JimothyJohn/wafer-flower/stl/dxf/02b_tail.dxf

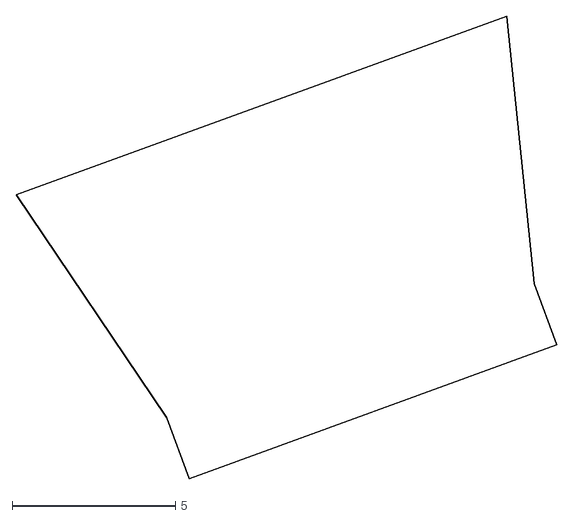
[picture p17: CAD file, 2026-07-26]
stl/dxf/02b_tail.dxf
16.6 x 14.2
