JimothyJohn/wafer-flower/stl/step/pinion.stp

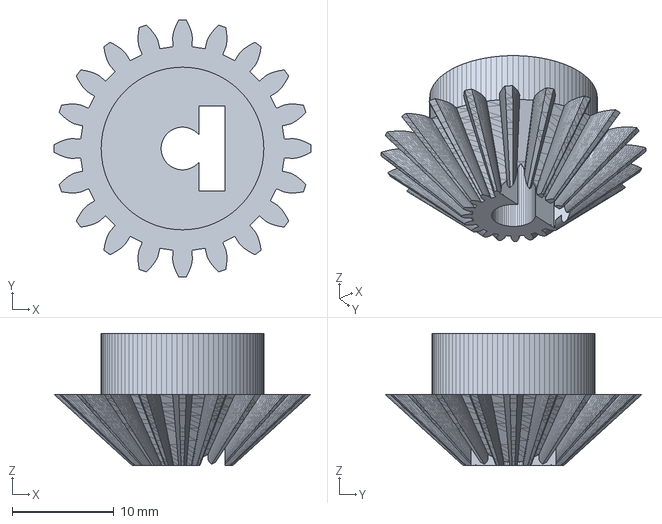
[picture p18: CAD file, 2026-07-28]
stl/step/pinion.stp
25.3 x 25.3 x 13.0 mm
