JimothyJohn/wafer-flower/stl/dxf/03_socket.dxf

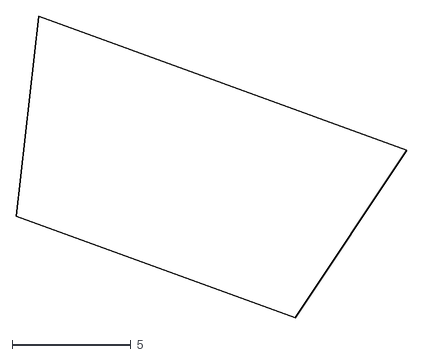
[picture p19: CAD file, 2026-07-20]
stl/dxf/03_socket.dxf
16.4 x 12.7
