JimothyJohn/wafer-flower/stl/segment_pair.stl

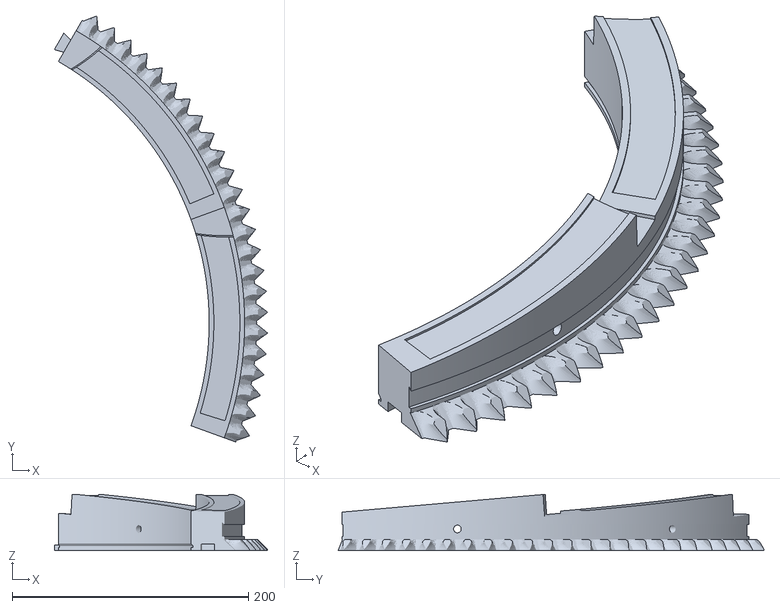
[picture p20: CAD file, 2026-07-28]
stl/segment_pair.stl
180.5 x 360.3 x 47.7
