JimothyJohn/wafer-flower/stl/step/bracket_bottom.stp

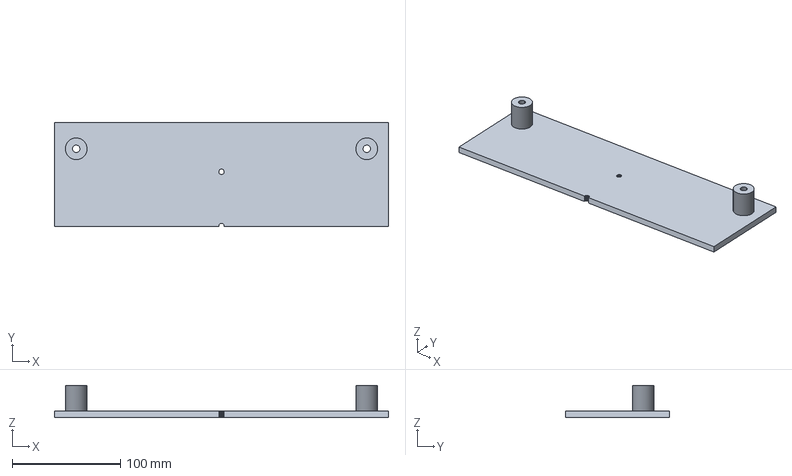
[picture p21: CAD file, 2026-07-27]
stl/step/bracket_bottom.stp
307.9 x 96.0 x 29.8 mm
