JimothyJohn/wafer-flower/stl/dxf/04_pocket.dxf

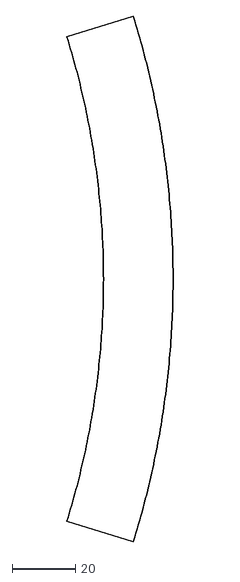
[picture p22: CAD file, 2026-07-20]
stl/dxf/04_pocket.dxf
33.6 x 166.1
