JimothyJohn/wafer-flower/stl/step/bracket_plate.stp

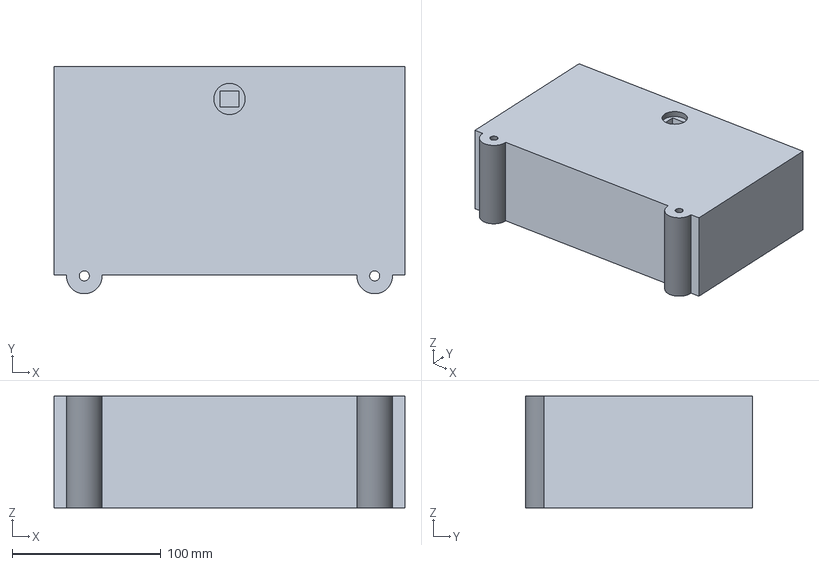
[picture p23: CAD file, 2026-07-26]
stl/step/bracket_plate.stp
236.0 x 153.0 x 75.2 mm
