JimothyJohn/wafer-flower/stl/halo_frame.stl

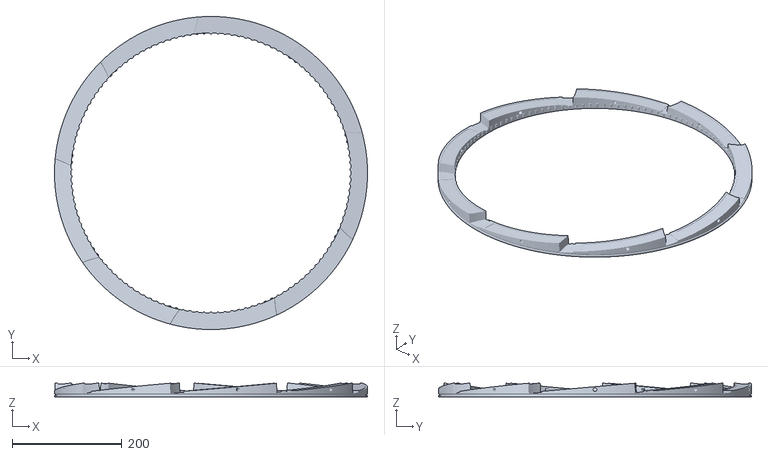
[picture p24: CAD file, 2026-07-25]
stl/halo_frame.stl
570.0 x 570.0 x 25.0
