JimothyJohn/wafer-flower/stl/step/segment.stp

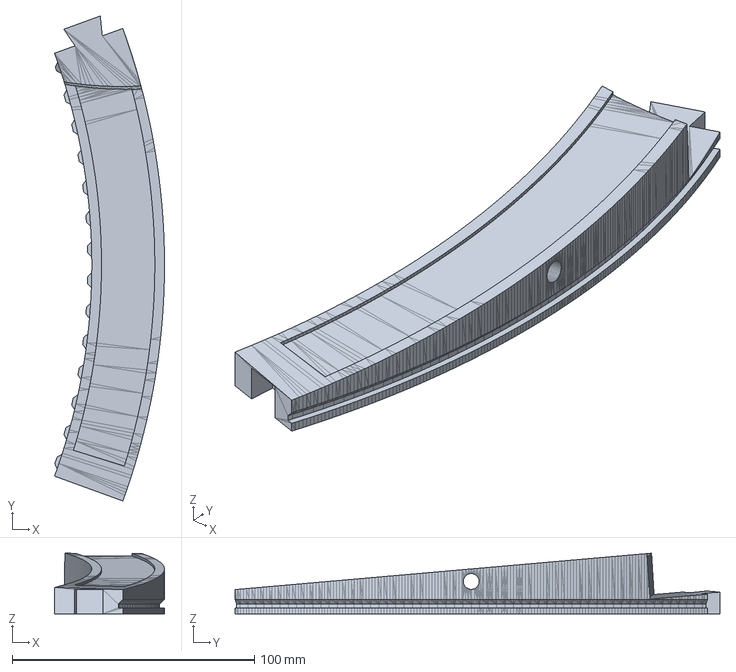
[picture p25: CAD file, 2026-07-25]
stl/step/segment.stp
45.4 x 200.1 x 25.0 mm
