JimothyJohn/wafer-flower/stl/bracket_fitcheck.stl

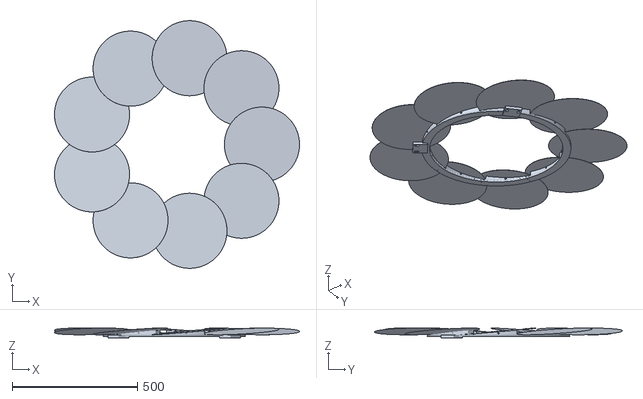
[picture p26: CAD file, 2026-07-25]
stl/bracket_fitcheck.stl
978.8 x 989.3 x 39.5
