JimothyJohn/wafer-flower/stl/step/wafer.stp

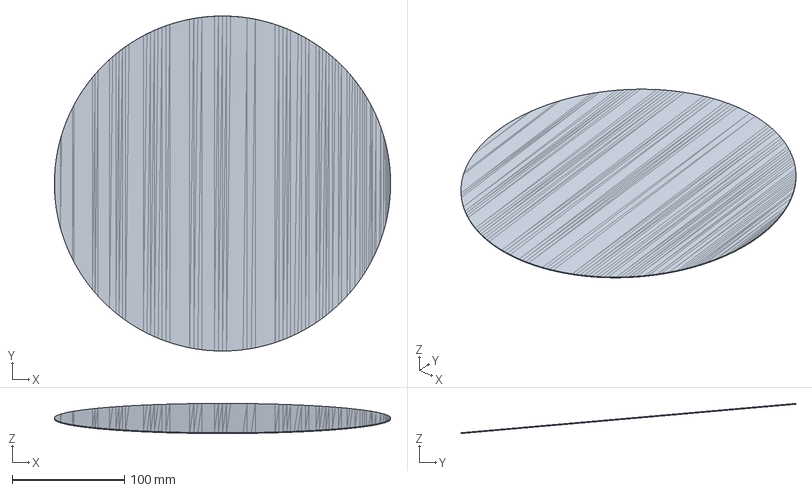
[picture p27: CAD file, 2026-07-23]
stl/step/wafer.stp
300.0 x 298.9 x 26.9 mm
