JimothyJohn/wafer-flower/docs/models/segment.stl

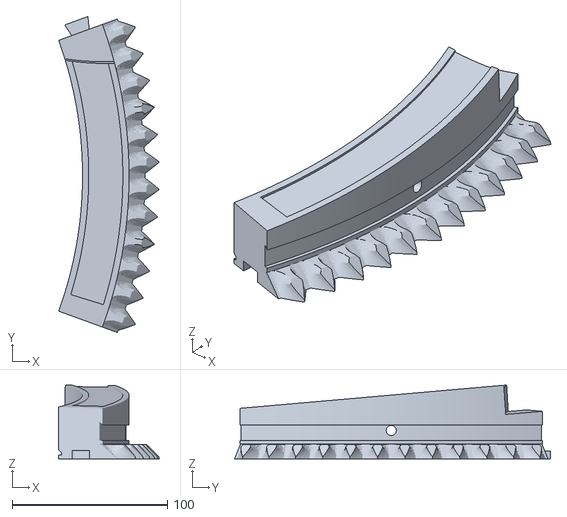
[picture p28: CAD file, 2026-07-28]
docs/models/segment.stl
64.9 x 203.6 x 47.7
