JimothyJohn/wafer-flower/docs/models/my_frame_segment.stl

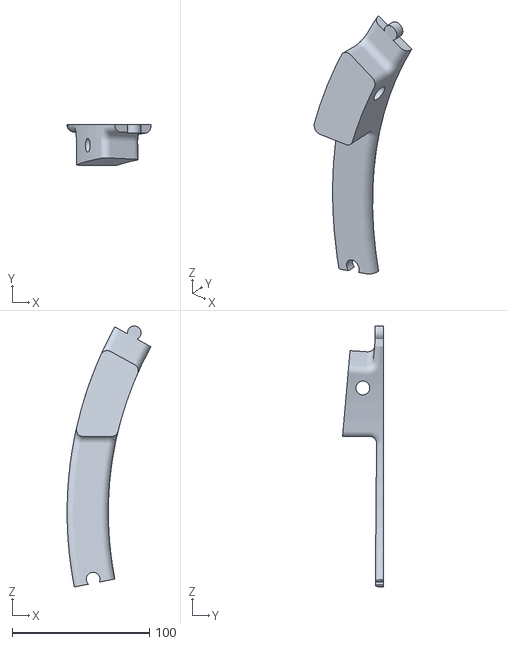
[picture p29: CAD file, 2026-07-22]
docs/models/my_frame_segment.stl
61.0 x 29.8 x 189.9
