JimothyJohn/wafer-flower/stl/drive_clamp.stl

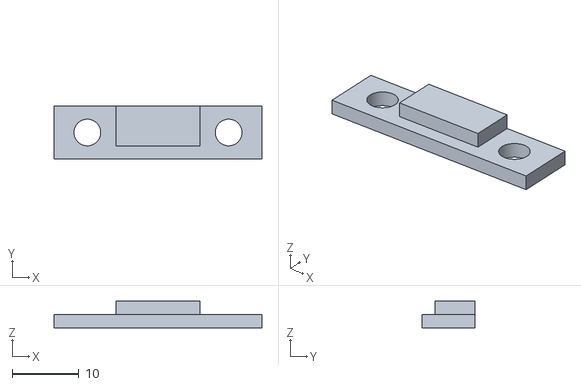
[picture p30: CAD file, 2026-07-23]
stl/drive_clamp.stl
31.2 x 8.00 x 4.00
