JimothyJohn/wafer-flower/stl/drive_plate.stl

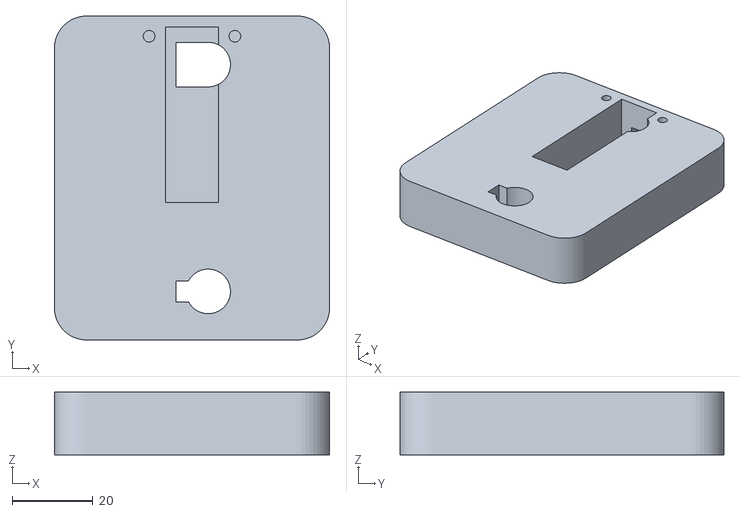
[picture p31: CAD file, 2026-07-23]
stl/drive_plate.stl
68.0 x 80.0 x 15.5
