JimothyJohn/wafer-flower/stl/drive_pinion.stl

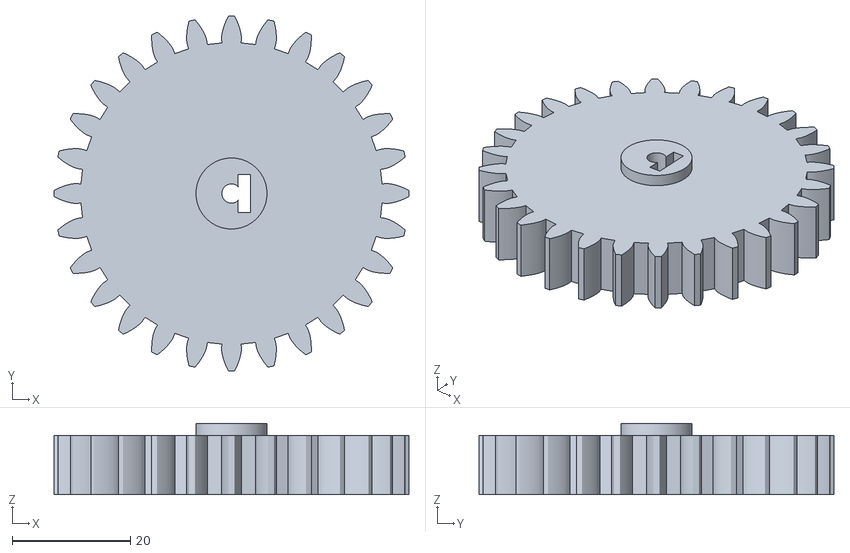
[picture p32: CAD file, 2026-07-23]
stl/drive_pinion.stl
60.0 x 60.0 x 12.0
