JimothyJohn/wafer-flower/stl/drive_fitcheck.stl

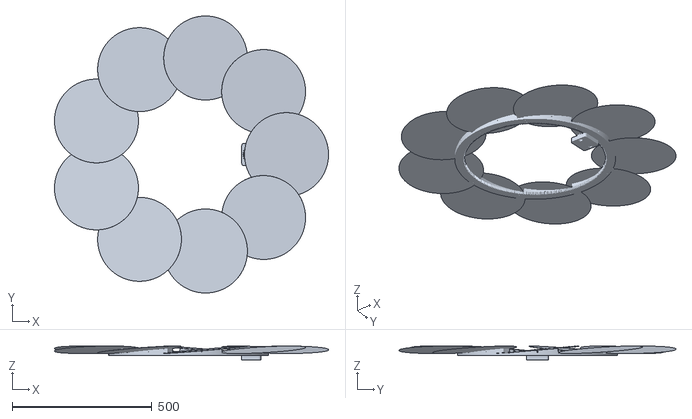
[picture p33: CAD file, 2026-07-23]
stl/drive_fitcheck.stl
978.8 x 989.3 x 50.0
