JimothyJohn/wafer-flower/docs/media/step1_segment.png

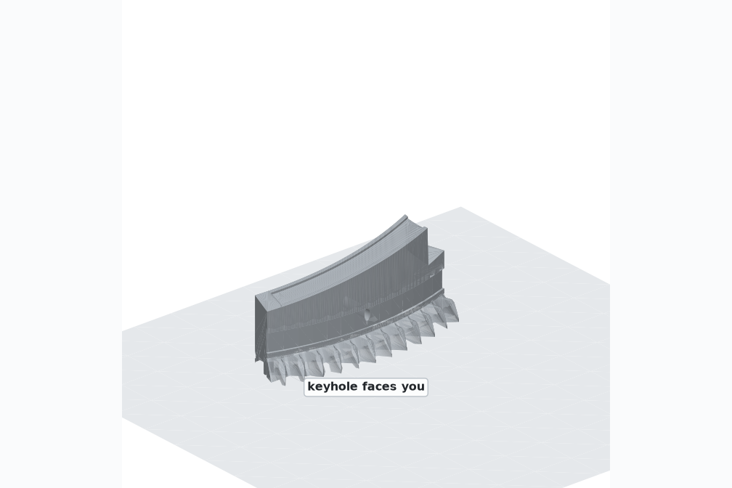
docs/media/step1_segment.png
