JimothyJohn/wafer-flower/docs/media/step3_outboard.png

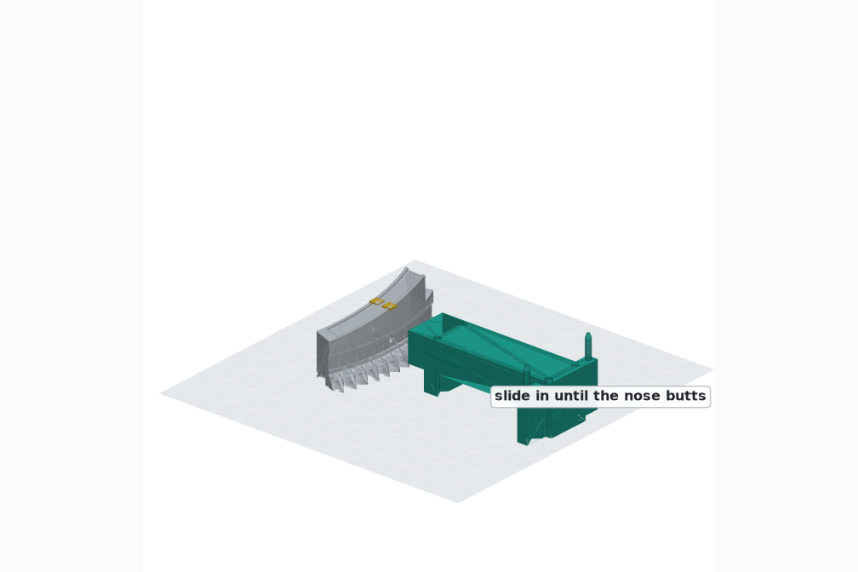
docs/media/step3_outboard.png
