JimothyJohn/wafer-flower/docs/media/step4_inboard.png

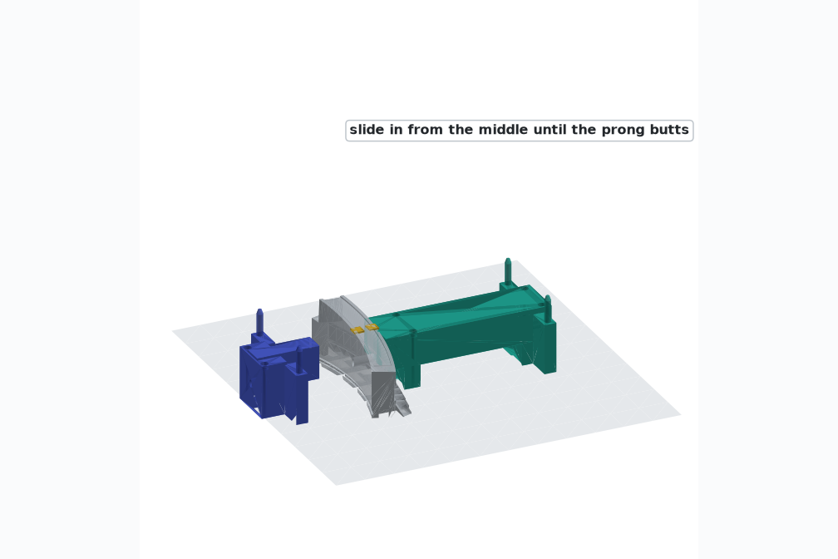
docs/media/step4_inboard.png
