JimothyJohn/wafer-flower/docs/media/step6_wafer.png

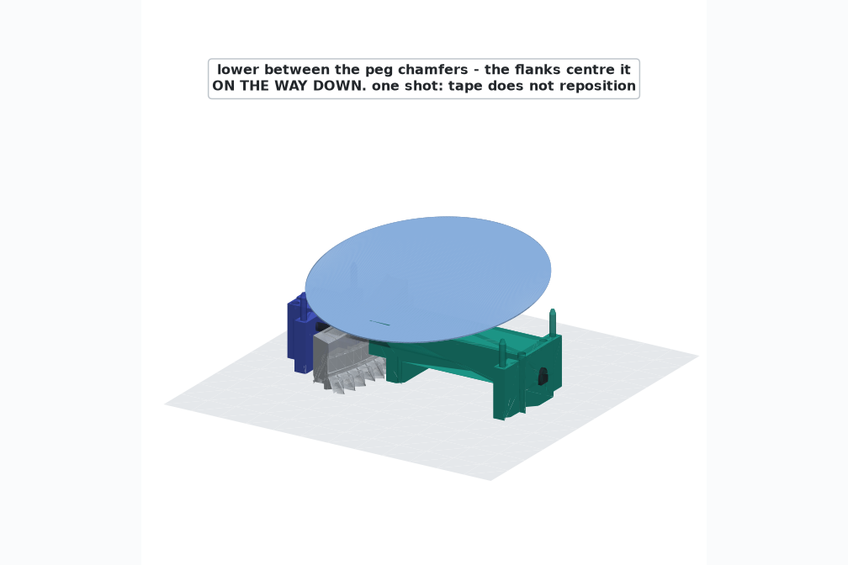
docs/media/step6_wafer.png
