JimothyJohn/wafer-flower/docs/media/step7_press.png

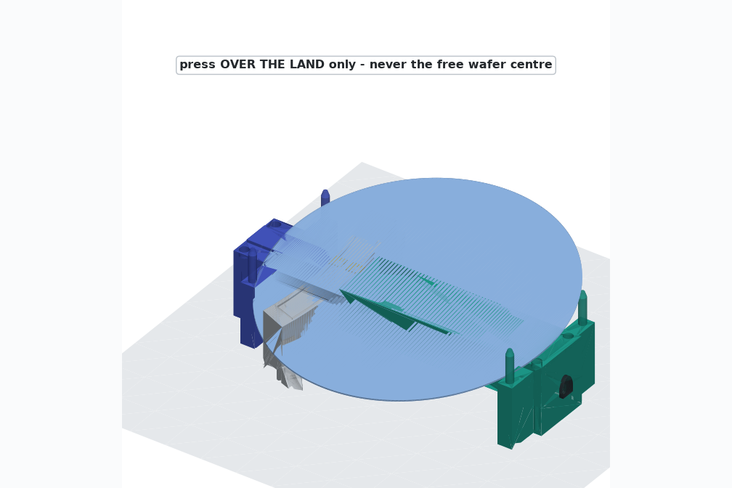
docs/media/step7_press.png
