JimothyJohn/wafer-flower/scripts/viewer_export.py

#!/usr/bin/env python3
"""
Wafer Halo — web viewer export + configuration interference gates.

The GitHub Pages viewer (docs/viewer.html) shows the REAL CAD, not a
re-derivation: this script exports every body in SCENE coordinates (halo axis
at the origin, bench at z_bot — the same frame cure_jig_fitcheck.stl uses)
into docs/models/, plus a manifest.json describing how the viewer may move
them: the jig open/close stroke, the wafer placement drop, and the 40-degree
station step for the glued ring.

Every configuration the viewer can show is CHECKED here first, on the real
solids, with boolean CSG — the script exits nonzero on any FAIL, and the
manifest carries the results so the page can display them:

  nominal    the full tape-jig suite from cure_jig_stl.run_checks (14 checks:
             fence/pin interference + capture funnel)
  travel     fences / pin swept open -> closed in steps must never
             touch the segment or the wafer at ANY point of the stroke
  placement  the wafer lowered onto the land along its plane normal with the
             jig open must clear the fences and the segment the whole way
  assembly   adjacent glued stations: segment/segment (dovetail), segment vs
             both neighbour wafers, wafer/wafer — all zero interference — and
             the DEPTH gate: the segment must stay >= 2.95 mm below the
             neighbour wafer's underside but come within 3.05 mm of it, i.e.
             the Rev B clearance cut exists and is neither missing nor
             over-deep (the same 3.000 mm gate T1 measures on the print)

    pip install manifold3d
    python3 scripts/viewer_export.py             # -> docs/models/
    python3 scripts/viewer_export.py --verify    # CI: checks + staleness gate
"""
from __future__ import annotations
import json, math, os, sys, argparse

sys.path.insert(0, os.path.dirname(os.path.abspath(__file__)))
from segment_stl import (PARAMS, Cfg, build_segment, build_wafer, write_stl,
                         report, wafer_cut, keyhole_z, Manifold, HAVE_MANIFOLD)
from cure_jig_stl import (JIG, Jig, build_outboard, build_inboard,
                          build_pin, run_checks)
from bracket_stl import (BRK, Brk, build_foot, build_top, build_shell,
                         wheel_at, pinion_at_top)

EPS = 1e-6
REPO = os.path.dirname(os.path.dirname(os.path.abspath(__file__)))
OUT_DIR = os.path.join(REPO, 'docs', 'models')

# Nick's OnShape rebuild, copied through byte-for-byte as a compare overlay.
# Expected in SCENE orientation (same frame as segment.stl); until it is, the
# viewer shows it floating wherever the export put it — mis-orientation is
# WARNED about, never gated: this is hand CAD in progress, not script output.
PASSTHRU_SRC = os.path.join(REPO, 'stl', 'my_frame_segment.stl')
PASSTHRU = dict(name='my_frame_segment', group='onshape', color=0x3E8E7E)

# Stroke lengths for the open/close animation, mm. Sized so every moving body
# fully clears the wafer footprint / keyhole; the travel sweep below PROVES it
# rather than trusting these numbers.
TRAVEL = dict(out=90.0, inboard=60.0, rod=130.0)
WAFER_LIFT = 40.0     # placement drop along the wafer plane normal
SWEEP_STEPS = 5       # positions checked across each stroke (incl. both ends)


_BRK_CACHE = {}
def _brk(cf):
    if id(cf) not in _BRK_CACHE:
        _BRK_CACHE[id(cf)] = Brk(cf)
    return _BRK_CACHE[id(cf)]


def build_scene(cf, j):
    """All bodies in scene coordinates, keyed by manifest part name."""
    pin, _, _ = build_pin(j)
    return {
        'segment':      (build_segment(cf),  'segment',  0xB9A87E),
        'wafer':        (build_wafer(cf, 0), 'wafer',    0x9AA6B2),
        'jig_outboard': (build_outboard(j),  'out',      0xD97742),
        'jig_inboard':  (build_inboard(j),   'inboard',  0x3E7CB1),
        # 'rod' stays the part/group name for the locating pin — the
        # manifest schema and viewer motion keys predate the tape rework
        'rod':          (pin,                'rod',      0x30343A),
        # top idler bracket in the hanging orientation (gravity -y):
        # shown by the viewers only in ring/halo contexts
        'bracket_static': (build_foot(_brk(cf)), 'bracket', 0x8A6D3B),
        'bracket_top':  (build_top(_brk(cf)),    'bracket', 0xB86038),
        'bracket_shell': (build_shell(_brk(cf)), 'bracket', 0x9A4A2E),
        'wheel_l':      (wheel_at(_brk(cf), 0),  'bracket', 0x6A7078),
        'wheel_r':      (wheel_at(_brk(cf), 1),  'bracket', 0x6A7078),
        'drive_pinion': (pinion_at_top(cf, _brk(cf)), 'bracket', 0xC2497B),
    }


def motion_vectors(cf):
    """Displacement (full stroke) per motion group. The wafer lifts along its
    own plane normal; jig groups run radially on the rod axis (x at a=0)."""
    _, _, n = cf.wafer_frame(0)
    return {
        'out':     [TRAVEL['out'], 0.0, 0.0],
        'inboard': [-TRAVEL['inboard'], 0.0, 0.0],
        'rod':     [TRAVEL['rod'], 0.0, 0.0],
        'wafer':   [WAFER_LIFT * n[0], WAFER_LIFT * n[1], WAFER_LIFT * n[2]],
        'segment': [0.0, 0.0, 0.0],
    }


def moved(solid, vec, t):
    return solid.translate([vec[0] * t, vec[1] * t, vec[2] * t])


def sweep_checks(cf, scene, vecs):
    """Jig opening stroke and wafer placement drop: zero contact throughout."""
    seg, waf = scene['segment'][0], scene['wafer'][0]
    fixed = seg + waf
    checks = []
    groups = {}
    for name, (solid, group, _) in scene.items():
        if group in ('out', 'inboard', 'rod'):
            groups[group] = groups.get(group, None) + solid if group in groups else solid
    for group, solid in groups.items():
        worst = 0.0
        for i in range(SWEEP_STEPS):
            t = i / (SWEEP_STEPS - 1)
            worst = max(worst, (moved(solid, vecs[group], t) ^ fixed).volume())
        checks.append(('travel', f'{group} stroke ({TRAVEL[group]:.0f} mm) vs '
                       f'segment+wafer, {SWEEP_STEPS} steps', worst, worst < EPS))
    # wafer drop with the jig fully open
    jig_open = sum((moved(groups[g], vecs[g], 1.0) for g in groups),
                   Manifold())
    fixed_open = seg + jig_open        # loop-invariant: hoisted out of the sweep
    worst = 0.0
    for i in range(SWEEP_STEPS):
        t = i / (SWEEP_STEPS - 1)
        w = moved(waf, vecs['wafer'], t)
        worst = max(worst, (w ^ fixed_open).volume())
    checks.append(('placement', f'wafer drop ({WAFER_LIFT:.0f} mm) vs segment '
                   f'+ open jig, {SWEEP_STEPS} steps', worst, worst < EPS))
    return checks


def assembly_checks(cf, seg, waf):
    """Adjacent glued stations. Rotational symmetry: station 0 vs 1 (and the
    trailing side via seg1 vs waf0) covers every pair in the ring."""
    seg1 = seg.rotate([0.0, 0.0, math.degrees(cf.sector)])
    waf1 = build_wafer(cf, 1)
    zero = [
        ('segment vs next segment (dovetail joint)', (seg ^ seg1).volume()),
        ('segment vs leading neighbour wafer',       (seg ^ waf1).volume()),
        ('segment vs trailing neighbour wafer',      (seg1 ^ waf).volume()),
        ('wafer vs neighbour wafer',                 (waf ^ waf1).volume()),
    ]
    checks = [('assembly', n, v, v < EPS) for n, v in zero]
    # depth (z) clearance gate against the leading wafer's plane: material must
    # stay 2.95 mm clear of the wafer underside, yet exist within 3.05 mm —
    # proves the clearance cut is present and cut to depth (T1's 3.000 mm).
    probe = lambda d: (seg ^ wafer_cut(cf, 1, -(cf.wafer_T / 2 + d), cf.tall)).volume()
    v_clear, v_touch = probe(cf.clr - 0.05), probe(cf.clr + 0.05)
    checks.append(('assembly', f'depth clearance >= {cf.clr - 0.05:.2f} mm under '
                   'the neighbour wafer', v_clear, v_clear < EPS))
    checks.append(('assembly', f'clearance cut present (material within '
                   f'{cf.clr + 0.05:.2f} mm)', v_touch, v_touch > EPS))
    # the joint actually engages: nudge the neighbour 0.1 deg into station 0
    v_butt = (seg ^ seg1.rotate([0.0, 0.0, -0.1])).volume()
    checks.append(('assembly', 'segments butt at the joint (0.1 deg nudge '
                   'contacts)', v_butt, v_butt > EPS))
    return checks


def build_all(cf, j):
    scene = build_scene(cf, j)
    vecs = motion_vectors(cf)

    print('nominal: tape-jig suite (cure_jig_stl.run_checks)')
    seg, waf = scene['segment'][0], scene['wafer'][0]
    nominal_ok = run_checks(j, seg, waf, scene['jig_outboard'][0],
                            scene['jig_inboard'][0], scene['rod'][0])
    checks = [('nominal', 'tape-jig fence/pin + capture suite (14 checks)',
               0.0 if nominal_ok else 1.0, nominal_ok)]
    checks += sweep_checks(cf, scene, vecs)
    checks += assembly_checks(cf, seg, waf)

    print('\ntravel / placement / assembly:')
    for grp, name, v, ok in checks[1:]:
        print(f"    {'PASS' if ok else 'FAIL':4}  [{grp}] {name:64} {v:10.4f}")
    return scene, vecs, checks


def stl_stats(path):
    """Tri count, bbox, and volume (divergence theorem) of a binary STL."""
    import struct
    with open(path, 'rb') as f:
        f.read(80)
        n = struct.unpack('<I', f.read(4))[0]
        lo, hi, vol6 = [1e30] * 3, [-1e30] * 3, 0.0
        for _ in range(n):
            rec = f.read(50)
            p = [struct.unpack('<3f', rec[12 + v * 12:24 + v * 12]) for v in range(3)]
            for v in p:
                for c in range(3):
                    lo[c] = min(lo[c], v[c]); hi[c] = max(hi[c], v[c])
            a, b, c3 = p
            vol6 += (a[0] * (b[1] * c3[2] - b[2] * c3[1])
                     + a[1] * (b[2] * c3[0] - b[0] * c3[2])
                     + a[2] * (b[0] * c3[1] - b[1] * c3[0]))
    return dict(tris=n, lo=lo, hi=hi, volume=abs(vol6) / 6.0)


def passthrough_entry(cf, seg):
    """Manifest entry for the OnShape overlay, or None if the file is absent.
    Warns (never fails) when its bbox is nowhere near the scene segment's —
    the tell of a raw Y-up OnShape export that still needs re-orienting."""
    if not os.path.exists(PASSTHRU_SRC):
        return None
    st = stl_stats(PASSTHRU_SRC)
    sb = seg.bounding_box()
    centred = all(abs((st['lo'][i] + st['hi'][i]) / 2 - (sb[i] + sb[i + 3]) / 2) < 60
                  for i in range(3))
    if not centred:
        print(f"\nWARNING: {os.path.basename(PASSTHRU_SRC)} bbox "
              f"{[round(x, 1) for x in st['lo']]}..{[round(x, 1) for x in st['hi']]} "
              f"is not in scene orientation (segment sits at "
              f"{[round(sb[i], 1) for i in range(3)]}..{[round(sb[i + 3], 1) for i in range(3)]}). "
              f"Overlay will float until it is re-exported in the same frame.")
    return {'file': f"{PASSTHRU['name']}.stl", 'name': PASSTHRU['name'],
            'group': PASSTHRU['group'], 'color': f"#{PASSTHRU['color']:06X}",
            'volume_cm3': round(st['volume'] / 1000.0, 3),
            'passthrough': True, 'oriented': centred}


def make_manifest(cf, scene, vecs, checks, volumes):
    return {
        'source': 'scripts/viewer_export.py',
        'params': {k: cf.p[k] for k in PARAMS},
        'sector_deg': math.degrees(cf.sector),
        'keyhole_z': keyhole_z(cf),
        'z_bot': cf.z_bot,
        'parts': [{'file': f'{name}.stl', 'name': name, 'group': group,
                   'color': f'#{color:06X}',
                   'volume_cm3': round(volumes[name] / 1000.0, 3)}
                  for name, (_, group, color) in scene.items()],
        'motion': {g: {'vector': [round(c, 4) for c in v]}
                   for g, v in vecs.items() if any(abs(c) > 0 for c in v)},
        'checks': [{'group': g, 'name': n, 'value_mm3': round(v, 4), 'pass': ok}
                   for g, n, v, ok in checks],
    }


def main():
    if not HAVE_MANIFOLD:
        sys.exit('needs manifold3d for STL output:  pip install manifold3d')
    ap = argparse.ArgumentParser(description='Wafer Halo — viewer model export')
    ap.add_argument('-o', '--out', default=OUT_DIR)
    ap.add_argument('--verify', action='store_true',
                    help='CI gate: run every check and compare against the '
                         'committed manifest instead of writing files')
    for k, v in {**PARAMS, **JIG}.items():
        ap.add_argument(f'--{k}', type=type(v), default=None)
    a = ap.parse_args()
    cf = Cfg(**{k: getattr(a, k) for k in PARAMS if getattr(a, k) is not None})
    j = Jig(cf, **{k: getattr(a, k) for k in JIG if getattr(a, k) is not None})

    scene, vecs, checks = build_all(cf, j)
    ok = all(c[3] for c in checks)
    volumes = {name: solid.volume() for name, (solid, _, _) in scene.items()}
    manifest = make_manifest(cf, scene, vecs, checks, volumes)
    passthru = passthrough_entry(cf, scene['segment'][0])
    if passthru:
        manifest['parts'].append(passthru)

    if a.verify:
        mpath = os.path.join(a.out, 'manifest.json')
        try:
            with open(mpath) as f:
                committed = json.load(f)
        except FileNotFoundError:
            sys.exit(f'FAIL: {mpath} missing — run scripts/viewer_export.py')
        stale = []
        if committed.get('params') != manifest['params']:
            stale.append('params differ')
        want = {p['file'] for p in manifest['parts']}
        have = {p['file'] for p in committed.get('parts', [])}
        if want != have:
            stale.append(f'part list differs: {sorted(want ^ have)}')
        else:
            got = {p['name']: p['volume_cm3'] for p in committed['parts']}
            for p in manifest['parts']:
                ref = got.get(p['name'], 0.0)
                # volumes, not bytes: float last-bits differ across platforms
                if abs(ref - p['volume_cm3']) > max(0.002 * p['volume_cm3'], 0.005):
                    stale.append(f"{p['name']} volume {ref} vs {p['volume_cm3']}")
        for f in sorted(want):
            if not os.path.exists(os.path.join(a.out, f)):
                stale.append(f'{f} missing from {a.out}')
        if passthru:
            # a byte-for-byte copy, so bytes ARE comparable here (unlike the
            # regenerated meshes above)
            dst = os.path.join(a.out, passthru['file'])
            if os.path.exists(dst):
                with open(PASSTHRU_SRC, 'rb') as fa, open(dst, 'rb') as fb:
                    if fa.read() != fb.read():
                        stale.append(f"{passthru['file']} differs from "
                                     f"stl/{passthru['file']} — re-copy")
        # the file:// bundle must mirror the committed manifest + STL bytes
        # exactly (both are committed, so bytes ARE comparable)
        jpath = os.path.join(a.out, 'models_data.js')
        if not os.path.exists(jpath):
            stale.append('models_data.js missing — rerun viewer_export.py')
        elif not stale:
            with open(jpath) as f:
                if f.read() != models_data_js(a.out, committed):
                    stale.append('models_data.js does not match the committed '
                                 'manifest/STLs — rerun viewer_export.py')
        print()
        if stale:
            print('STALE — docs/models does not match the scripts. '
                  'Rerun scripts/viewer_export.py and commit:')
            for s in stale:
                print(f'    {s}')
        print('ALL CHECKS PASS' if ok and not stale else 'FAILURES ABOVE')
        return 0 if ok and not stale else 1

    os.makedirs(a.out, exist_ok=True)
    print()
    for name, (solid, _, _) in scene.items():
        fname = f'{name}.stl'
        bodies = write_stl(solid, os.path.join(a.out, fname))
        report(fname, solid, bodies, f"group {scene[name][1]}")
    if passthru:
        import shutil
        shutil.copyfile(PASSTHRU_SRC, os.path.join(a.out, passthru['file']))
        print(f"  {passthru['file']:20} copied through from stl/ "
              f"({'scene-oriented' if passthru['oriented'] else 'NOT yet in scene orientation'})")
    with open(os.path.join(a.out, 'manifest.json'), 'w') as f:
        json.dump(manifest, f, indent=1)
        f.write('\n')
    js = models_data_js(a.out, manifest)
    with open(os.path.join(a.out, 'models_data.js'), 'w') as f:
        f.write(js)
    print(f"  models_data.js       base64 bundle for file:// viewing "
          f"({len(js) // 1024} kB)")
    print(f"\n{'ALL CHECKS PASS' if ok else 'CHECK FAILURES ABOVE — do not publish'}")
    print(f'Wrote to {os.path.abspath(a.out)}/')
    return 0 if ok else 1


def models_data_js(outdir, manifest):
    """Single-file base64 bundle of the manifest + every part STL.

    Why it exists: fetch() is blocked under file://, so a double-clicked
    docs/index.html cannot load models/. A <script src> IS allowed under
    file://, so the viewer falls back to this bundle when fetch fails.
    Regenerated (and staleness-gated by --verify) alongside the STLs — the
    STLs stay authoritative and GitHub-previewable; this is a mirror."""
    import base64
    files = {}
    for p in manifest['parts']:
        with open(os.path.join(outdir, p['file']), 'rb') as f:
            files[p['file']] = base64.b64encode(f.read()).decode('ascii')
    return ('// generated by scripts/viewer_export.py — do not edit\n'
            'window.HALO_MODELS='
            + json.dumps({'manifest': manifest, 'files': files})
            + ';\n')


if __name__ == '__main__':
    sys.exit(main())
